TheCosmicNebula/ClioIVDigitalDash/4 - Software/3 - RealDash UI/images/car.jpg

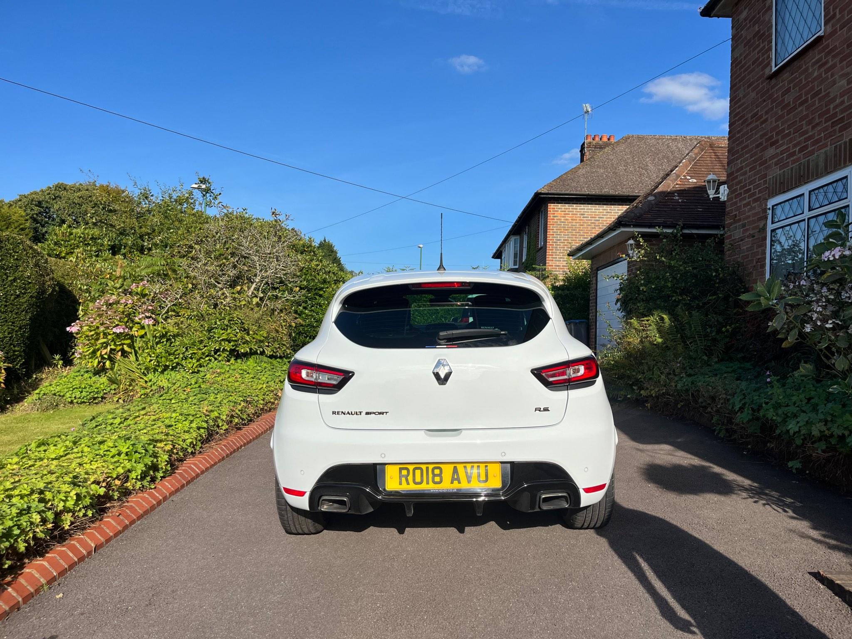
4 - Software/3 - RealDash UI/images/car.jpg
