TheCosmicNebula/ClioIVDigitalDash/1 - Physical Unit/1 - Pi/Raspberry-Pi-5-Technical-Drawing.jpg

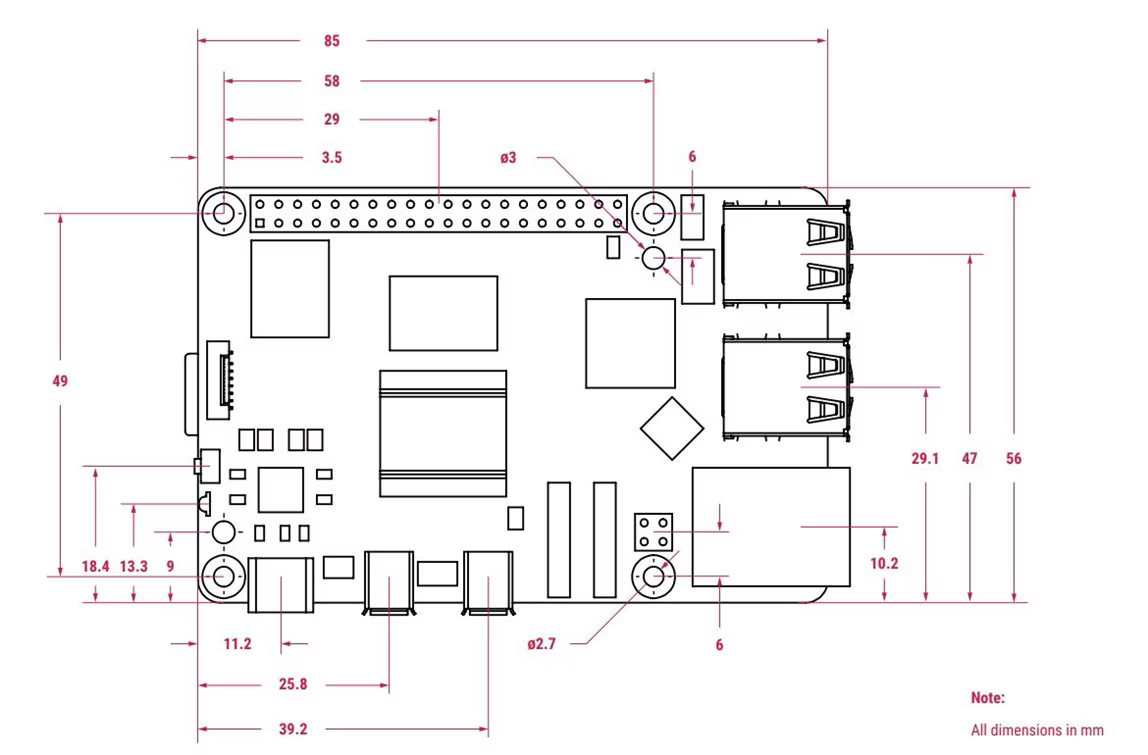
1 - Physical Unit/1 - Pi/Raspberry-Pi-5-Technical-Drawing.jpg
