TheCosmicNebula/ClioIVDigitalDash/1 - Physical Unit/3 - Label/561815/label.png

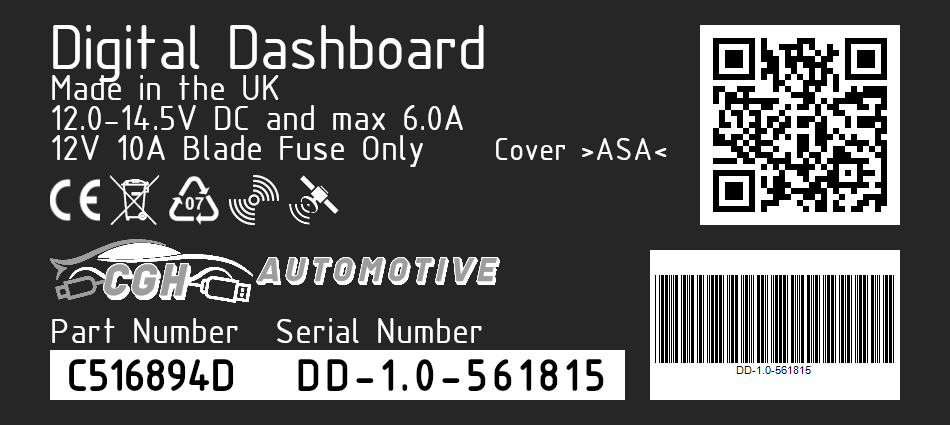
1 - Physical Unit/3 - Label/561815/label.png
