TheCosmicNebula/ClioIVDigitalDash/1 - Physical Unit/4 - Reference/rear.jpg

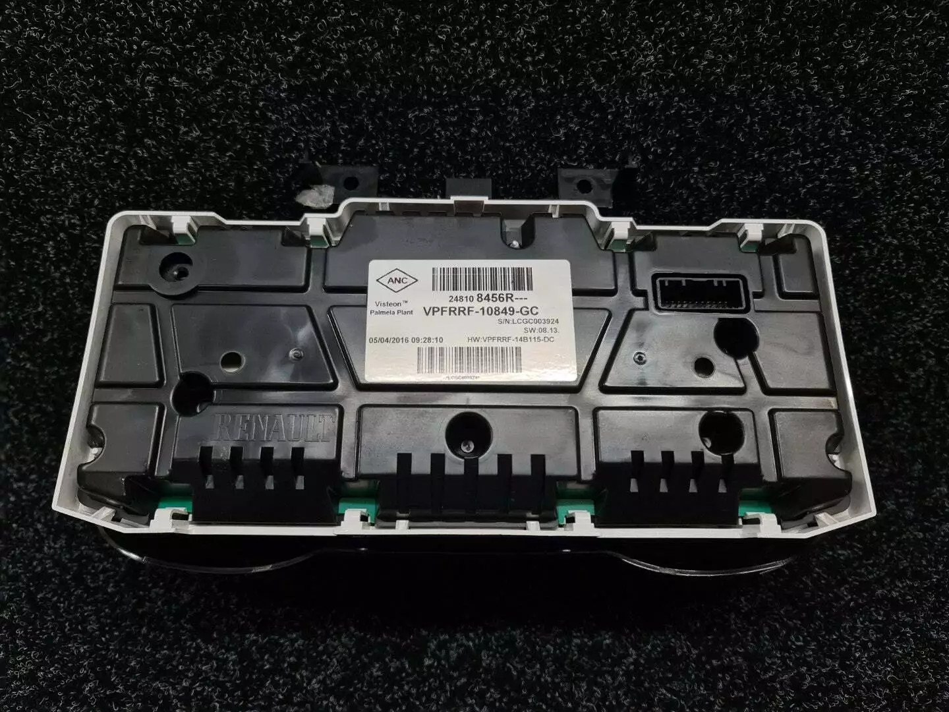
1 - Physical Unit/4 - Reference/rear.jpg
