TheCosmicNebula/ClioIVDigitalDash/2 - Custom UI/20240502_194230.jpg

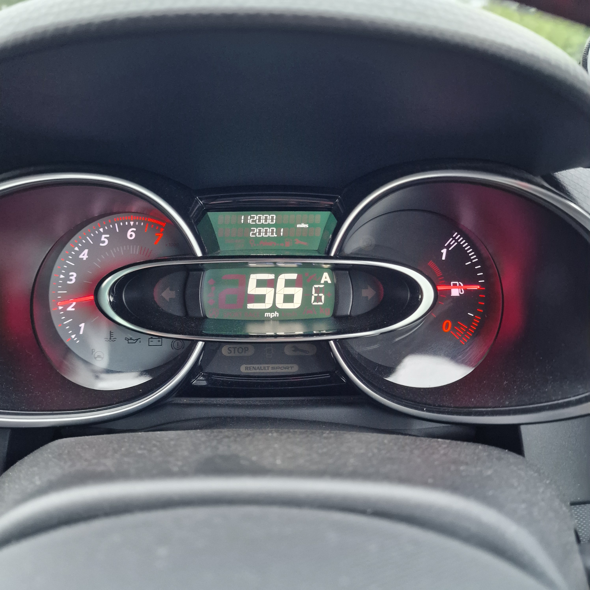
2 - Custom UI/20240502_194230.jpg
