TheCosmicNebula/ClioIVDigitalDash/2 - Custom UI/example_ui.jpg

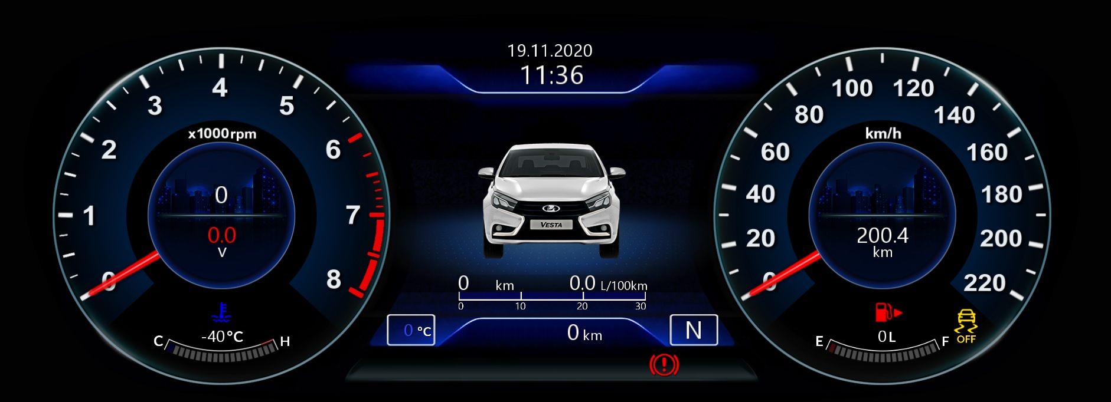
2 - Custom UI/example_ui.jpg
