TheCosmicNebula/ClioIVDigitalDash/2 - Custom UI/pixelcut-export.jpeg

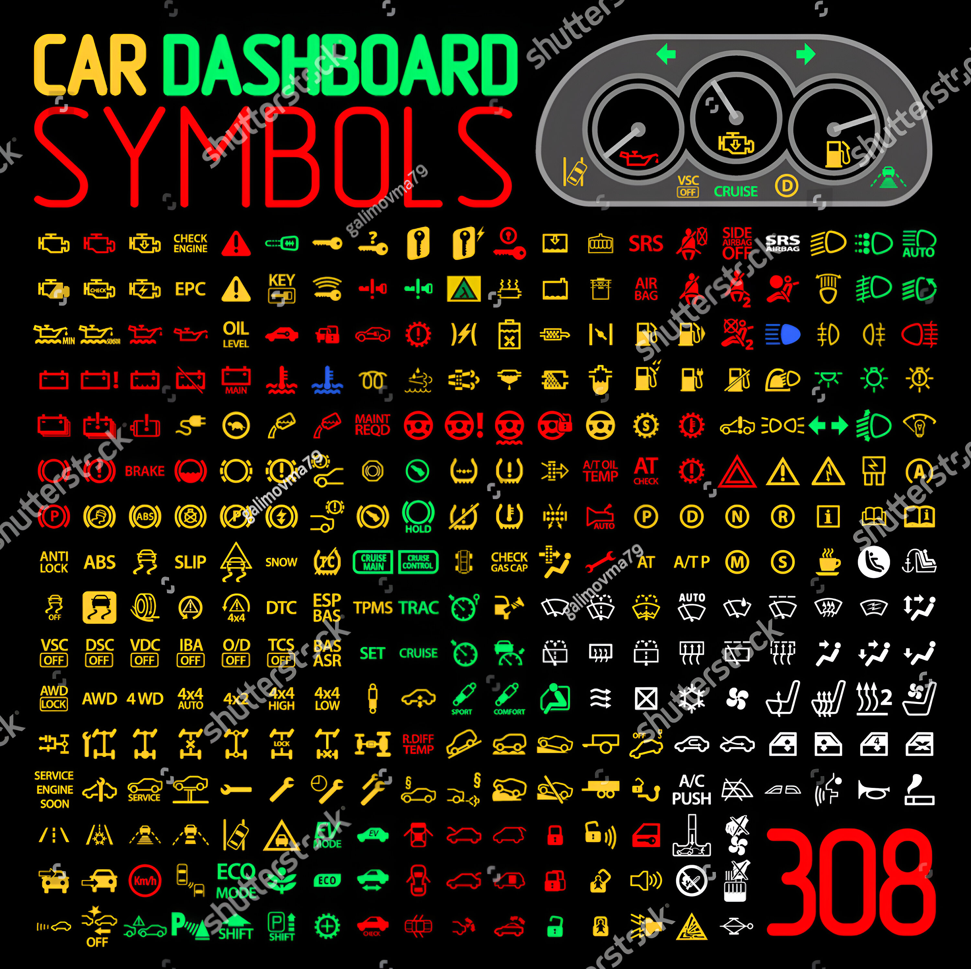
2 - Custom UI/pixelcut-export.jpeg
