TheCosmicNebula/ClioIVDigitalDash/2 - Custom UI/pixelcut-export.png

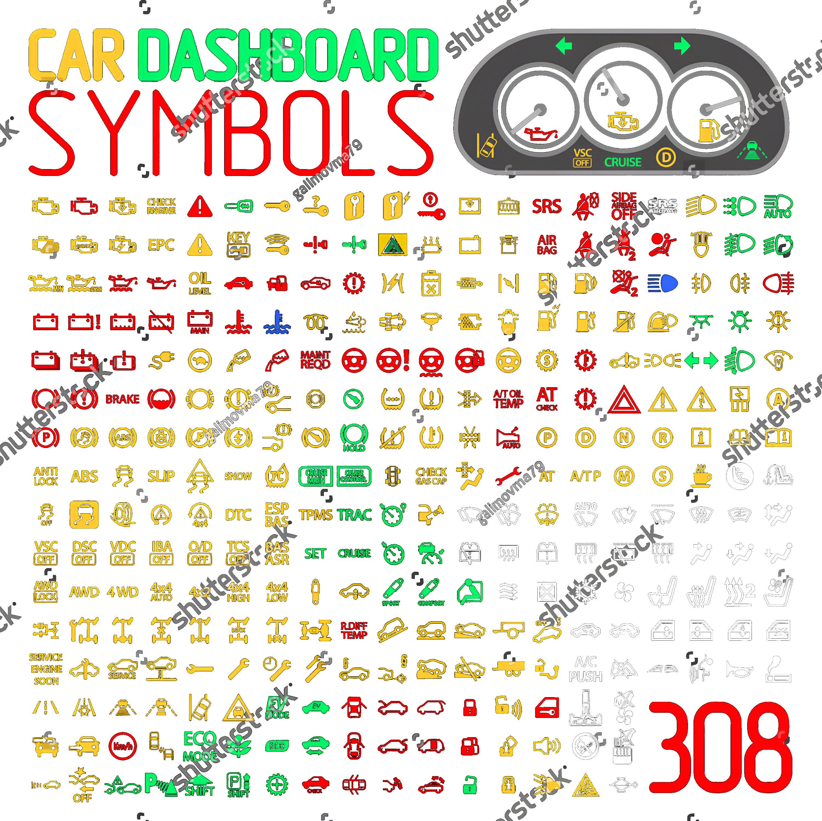
2 - Custom UI/pixelcut-export.png
