TheCosmicNebula/ClioIVDigitalDash/2 - Custom UI/vector-collection-car-dashboard-panel-600w-329151206.webp

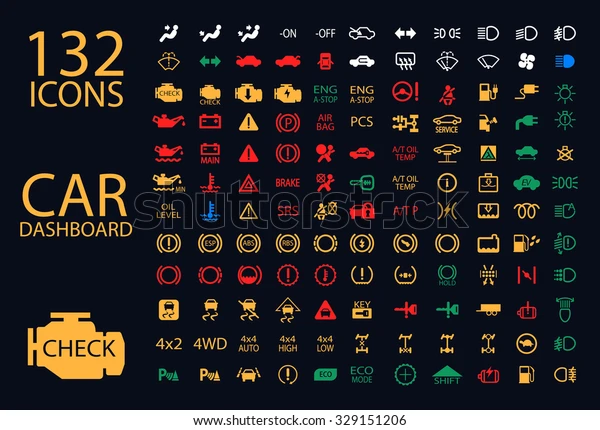
2 - Custom UI/vector-collection-car-dashboard-panel-600w-329151206.webp
