TheCosmicNebula/ClioIVDigitalDash/3 - Startup Animation/boot_darkmode_v2.gif

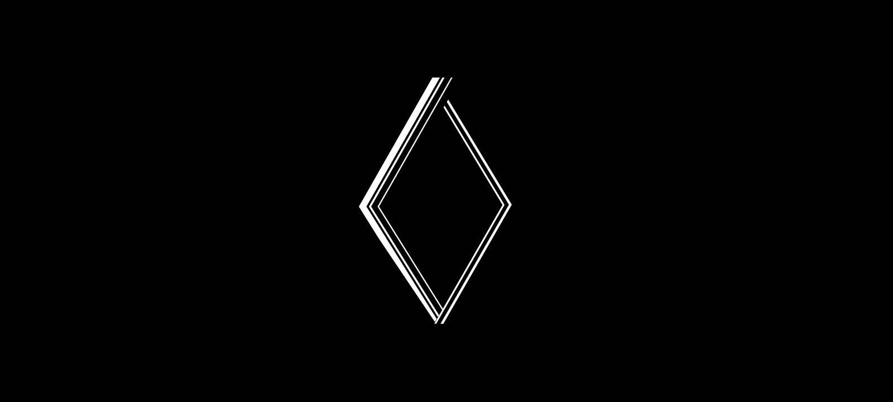
3 - Startup Animation/boot_darkmode_v2.gif
