TheCosmicNebula/ClioIVDigitalDash/3 - Startup Animation/cgh_automotive.png

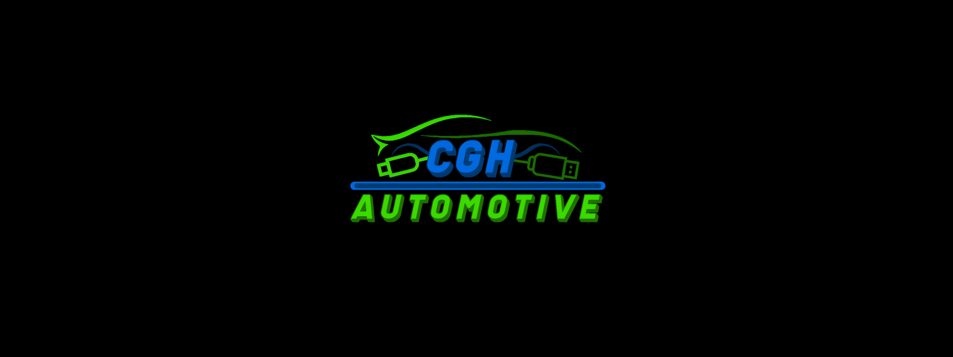
3 - Startup Animation/cgh_automotive.png
