TheCosmicNebula/ClioIVDigitalDash/3 - Startup Animation/reference/original_animation.gif

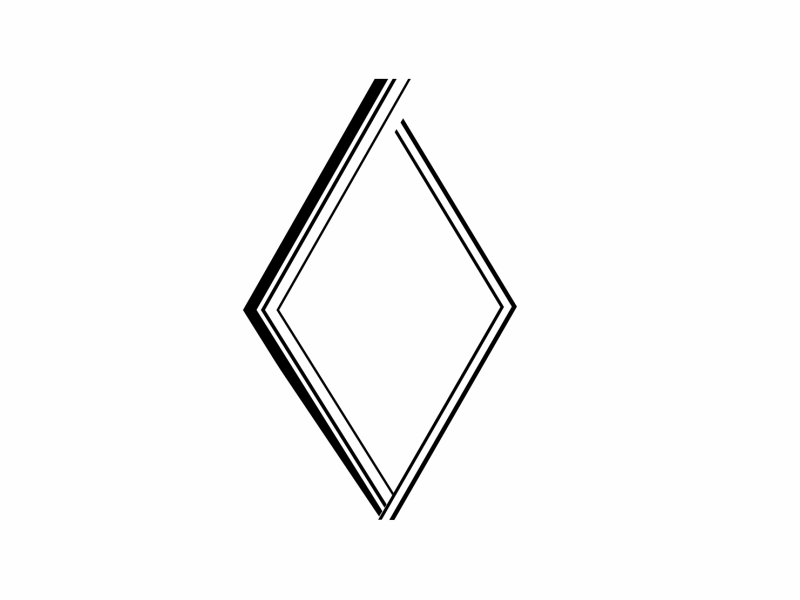
3 - Startup Animation/reference/original_animation.gif
