TheCosmicNebula/ClioIVDigitalDash/3 - Startup Animation/ss/boot_v1.gif

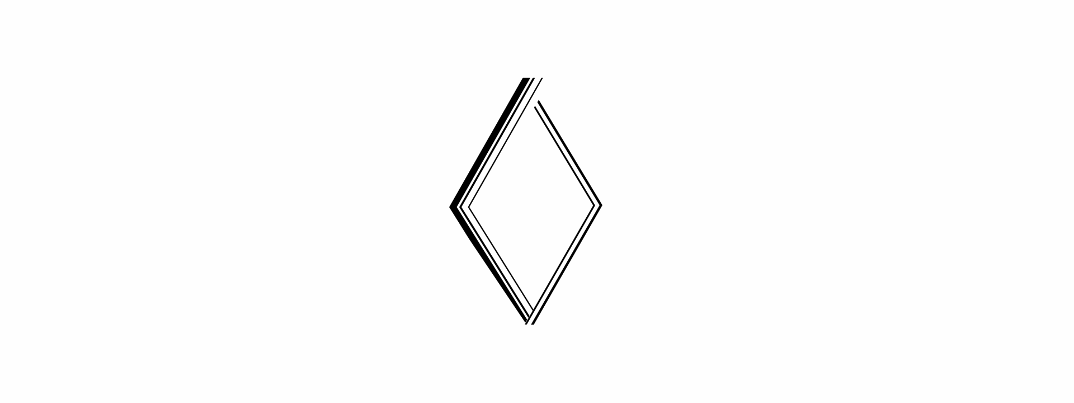
3 - Startup Animation/ss/boot_v1.gif
