TheCosmicNebula/ClioIVDigitalDash/3 - Startup Animation/TheCN.png

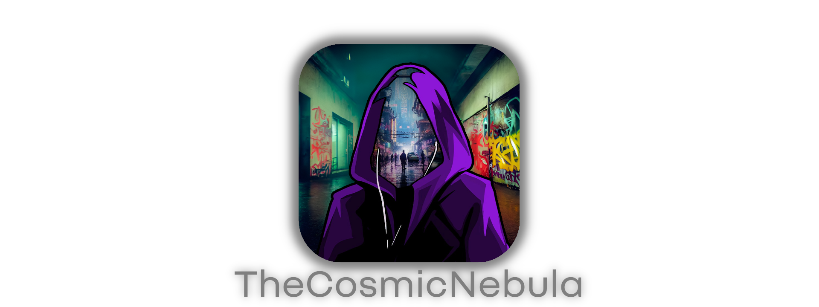
3 - Startup Animation/TheCN.png
