TheCosmicNebula/ClioIVDigitalDash/4 - Software/3 - RealDash UI/images/cruise_control.png

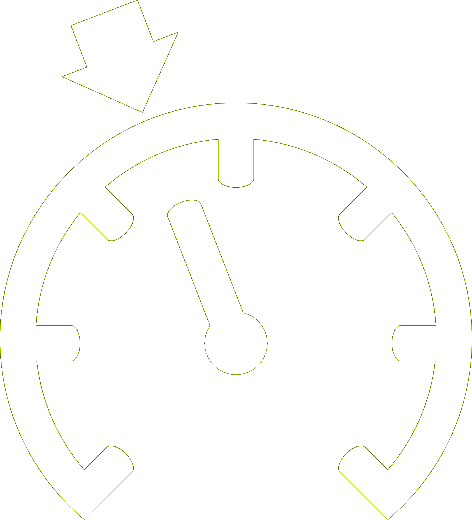
4 - Software/3 - RealDash UI/images/cruise_control.png
