TheCosmicNebula/ClioIVDigitalDash/4 - Software/3 - RealDash UI/images/Cruise_Control.svg.png

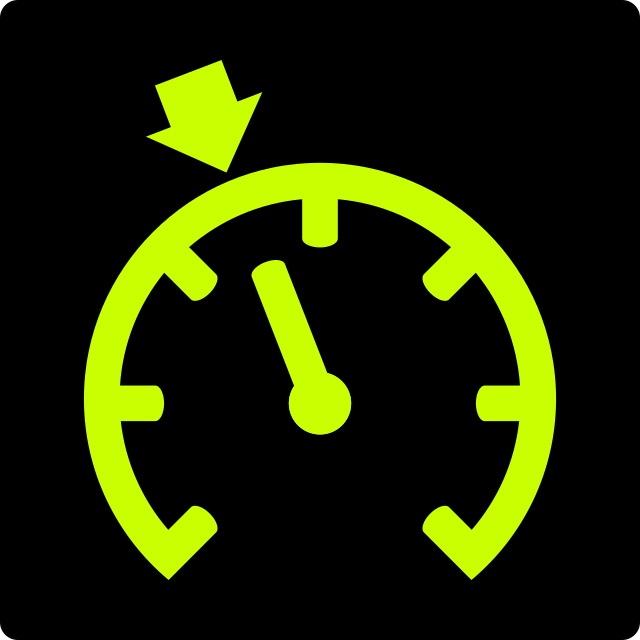
4 - Software/3 - RealDash UI/images/Cruise_Control.svg.png
