TheCosmicNebula/ClioIVDigitalDash/4 - Software/3 - RealDash UI/images/final/abs.png

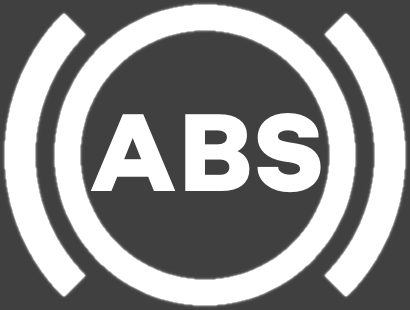
4 - Software/3 - RealDash UI/images/final/abs.png
