TheCosmicNebula/ClioIVDigitalDash/4 - Software/3 - RealDash UI/images/final/airbag.png

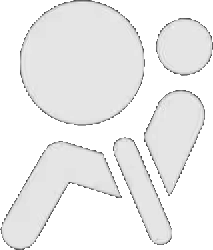
4 - Software/3 - RealDash UI/images/final/airbag.png
