TheCosmicNebula/ClioIVDigitalDash/4 - Software/3 - RealDash UI/images/final/auto_lights.png

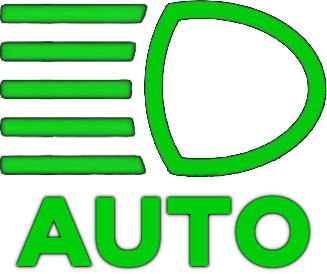
4 - Software/3 - RealDash UI/images/final/auto_lights.png
