TheCosmicNebula/ClioIVDigitalDash/4 - Software/3 - RealDash UI/images/final/auto_wipers.png

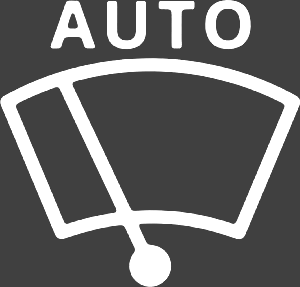
4 - Software/3 - RealDash UI/images/final/auto_wipers.png
