TheCosmicNebula/ClioIVDigitalDash/4 - Software/3 - RealDash UI/images/final/battery.png

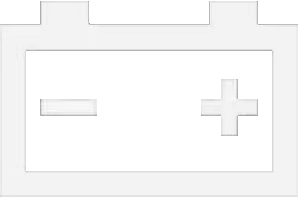
4 - Software/3 - RealDash UI/images/final/battery.png
