TheCosmicNebula/ClioIVDigitalDash/4 - Software/3 - RealDash UI/images/final/car_body.png

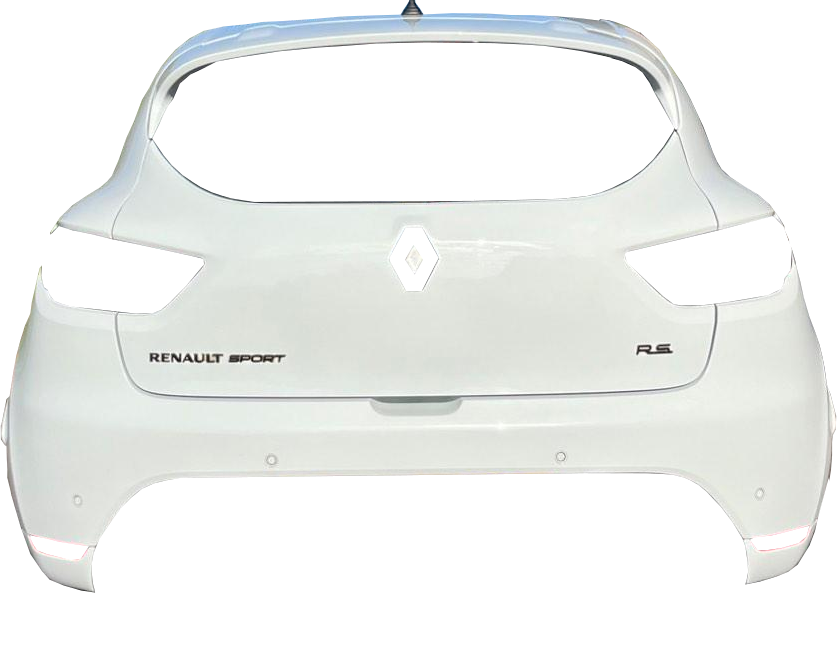
4 - Software/3 - RealDash UI/images/final/car_body.png
