TheCosmicNebula/ClioIVDigitalDash/4 - Software/3 - RealDash UI/images/final/check_engine.png

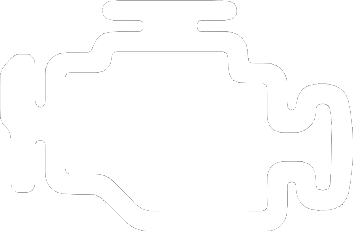
4 - Software/3 - RealDash UI/images/final/check_engine.png
