TheCosmicNebula/ClioIVDigitalDash/4 - Software/3 - RealDash UI/images/final/coolant_temp.png

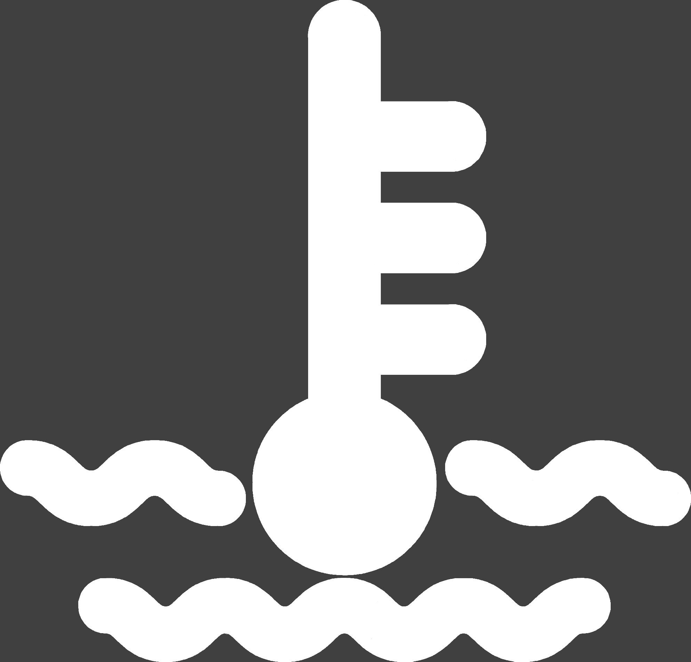
4 - Software/3 - RealDash UI/images/final/coolant_temp.png
