TheCosmicNebula/ClioIVDigitalDash/4 - Software/3 - RealDash UI/images/final/door_ajar.png

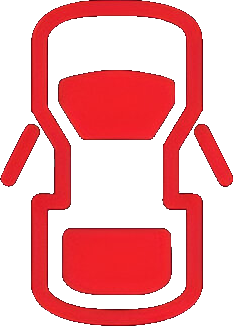
4 - Software/3 - RealDash UI/images/final/door_ajar.png
