TheCosmicNebula/ClioIVDigitalDash/4 - Software/3 - RealDash UI/images/final/door_ajar_4.png

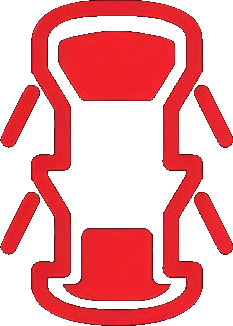
4 - Software/3 - RealDash UI/images/final/door_ajar_4.png
