TheCosmicNebula/ClioIVDigitalDash/4 - Software/3 - RealDash UI/images/final/door_ajar_boot_open.png

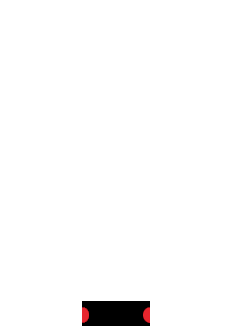
4 - Software/3 - RealDash UI/images/final/door_ajar_boot_open.png
