TheCosmicNebula/ClioIVDigitalDash/4 - Software/3 - RealDash UI/images/final/door_ajar_nsf_open.png

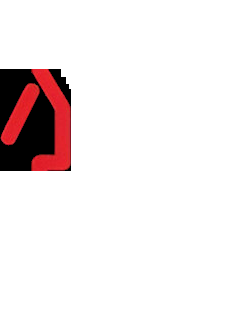
4 - Software/3 - RealDash UI/images/final/door_ajar_nsf_open.png
