TheCosmicNebula/ClioIVDigitalDash/4 - Software/3 - RealDash UI/images/final/esc_off.png

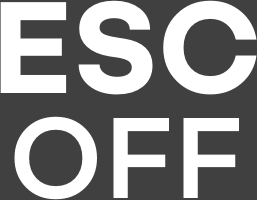
4 - Software/3 - RealDash UI/images/final/esc_off.png
