TheCosmicNebula/ClioIVDigitalDash/4 - Software/3 - RealDash UI/images/final/front_defrost.png

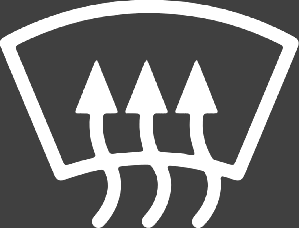
4 - Software/3 - RealDash UI/images/final/front_defrost.png
