TheCosmicNebula/ClioIVDigitalDash/4 - Software/3 - RealDash UI/images/final/front_fog.png

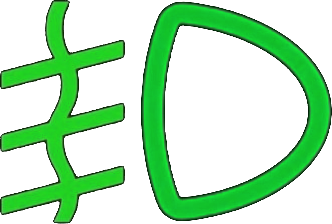
4 - Software/3 - RealDash UI/images/final/front_fog.png
