TheCosmicNebula/ClioIVDigitalDash/4 - Software/3 - RealDash UI/images/final/fuel.png

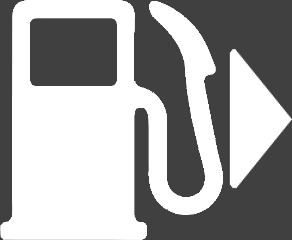
4 - Software/3 - RealDash UI/images/final/fuel.png
