TheCosmicNebula/ClioIVDigitalDash/4 - Software/3 - RealDash UI/images/final/fuel_low.png

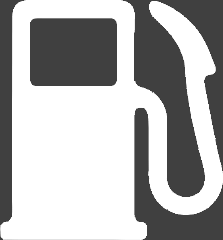
4 - Software/3 - RealDash UI/images/final/fuel_low.png
