TheCosmicNebula/ClioIVDigitalDash/4 - Software/3 - RealDash UI/images/final/handbrake.png

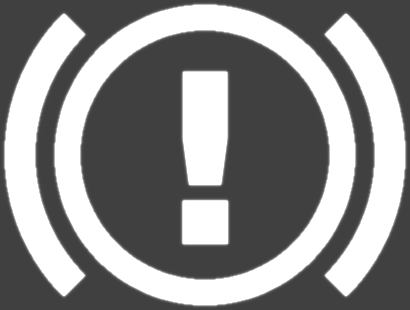
4 - Software/3 - RealDash UI/images/final/handbrake.png
