TheCosmicNebula/ClioIVDigitalDash/4 - Software/3 - RealDash UI/images/final/ice_warning.png

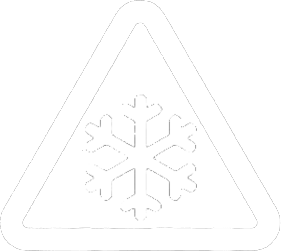
4 - Software/3 - RealDash UI/images/final/ice_warning.png
