TheCosmicNebula/ClioIVDigitalDash/4 - Software/3 - RealDash UI/images/final/lock.png

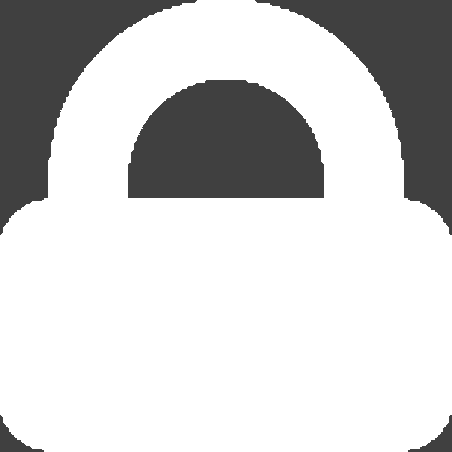
4 - Software/3 - RealDash UI/images/final/lock.png
