TheCosmicNebula/ClioIVDigitalDash/4 - Software/3 - RealDash UI/images/final/low_beam.png

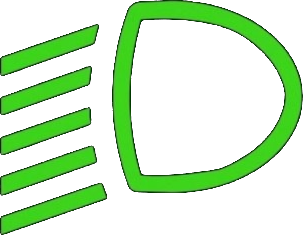
4 - Software/3 - RealDash UI/images/final/low_beam.png
