TheCosmicNebula/ClioIVDigitalDash/4 - Software/3 - RealDash UI/images/final/oil_pressure_w.png

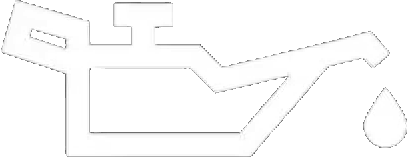
4 - Software/3 - RealDash UI/images/final/oil_pressure_w.png
