TheCosmicNebula/ClioIVDigitalDash/4 - Software/3 - RealDash UI/images/final/press_brake.png

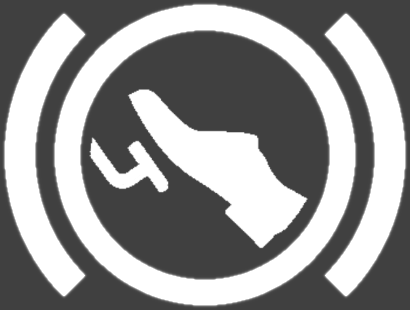
4 - Software/3 - RealDash UI/images/final/press_brake.png
