TheCosmicNebula/ClioIVDigitalDash/4 - Software/3 - RealDash UI/images/final/rear_defrost.png

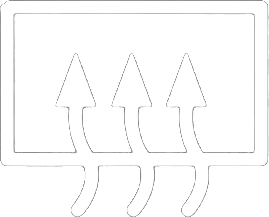
4 - Software/3 - RealDash UI/images/final/rear_defrost.png
