TheCosmicNebula/ClioIVDigitalDash/4 - Software/3 - RealDash UI/images/final/rear_fog.png

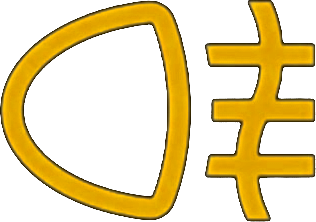
4 - Software/3 - RealDash UI/images/final/rear_fog.png
