TheCosmicNebula/ClioIVDigitalDash/4 - Software/3 - RealDash UI/images/final/rear_window_lock.png

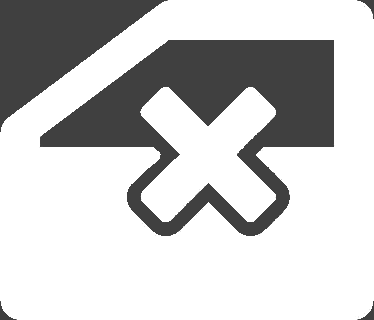
4 - Software/3 - RealDash UI/images/final/rear_window_lock.png
