TheCosmicNebula/ClioIVDigitalDash/4 - Software/3 - RealDash UI/images/final/renault_sport.png

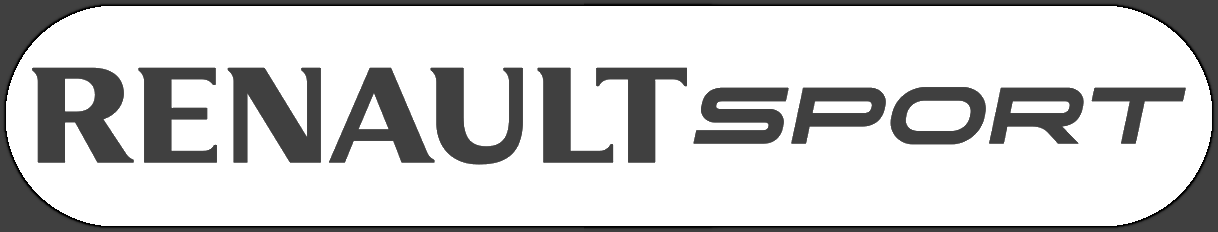
4 - Software/3 - RealDash UI/images/final/renault_sport.png
