TheCosmicNebula/ClioIVDigitalDash/4 - Software/3 - RealDash UI/images/final/seatbelt.png

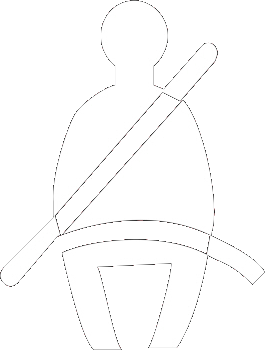
4 - Software/3 - RealDash UI/images/final/seatbelt.png
