TheCosmicNebula/ClioIVDigitalDash/4 - Software/3 - RealDash UI/images/final/side_lights.png

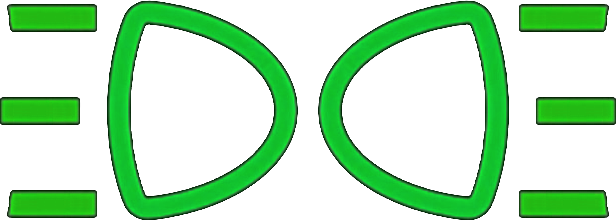
4 - Software/3 - RealDash UI/images/final/side_lights.png
