TheCosmicNebula/ClioIVDigitalDash/4 - Software/3 - RealDash UI/images/final/spanner.png

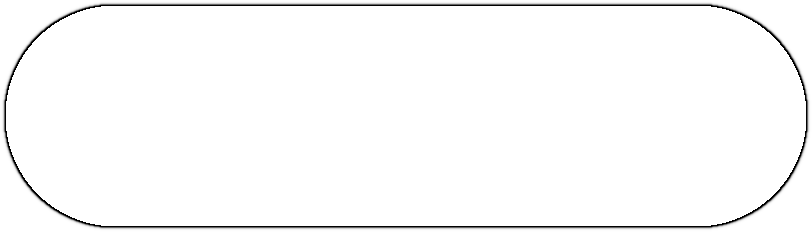
4 - Software/3 - RealDash UI/images/final/spanner.png
