TheCosmicNebula/ClioIVDigitalDash/4 - Software/3 - RealDash UI/images/final/steering.png

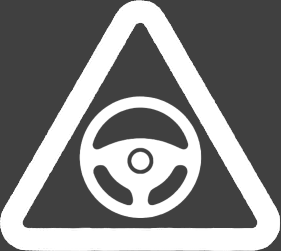
4 - Software/3 - RealDash UI/images/final/steering.png
