TheCosmicNebula/ClioIVDigitalDash/4 - Software/3 - RealDash UI/images/final/traction.png

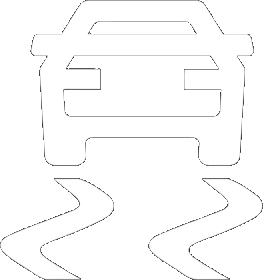
4 - Software/3 - RealDash UI/images/final/traction.png
