TheCosmicNebula/ClioIVDigitalDash/4 - Software/3 - RealDash UI/images/final/tyre_pressure.png

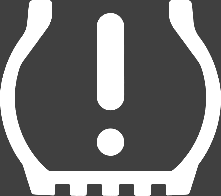
4 - Software/3 - RealDash UI/images/final/tyre_pressure.png
