TheCosmicNebula/ClioIVDigitalDash/4 - Software/3 - RealDash UI/images/source/arrows.webp

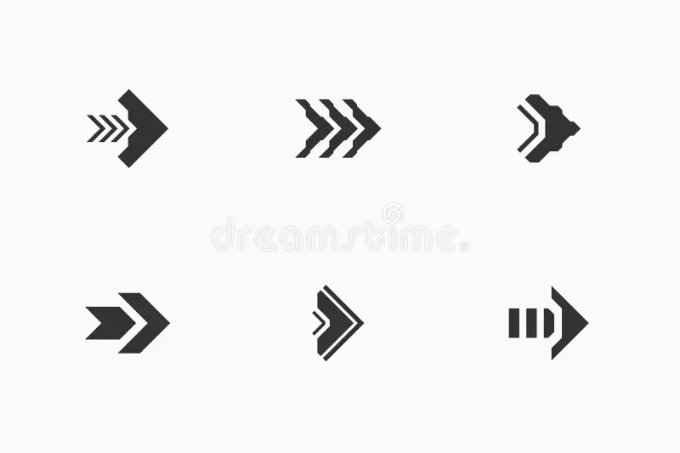
4 - Software/3 - RealDash UI/images/source/arrows.webp
