TheCosmicNebula/ClioIVDigitalDash/4 - Software/3 - RealDash UI/images/source/coolant_temperature.jpg

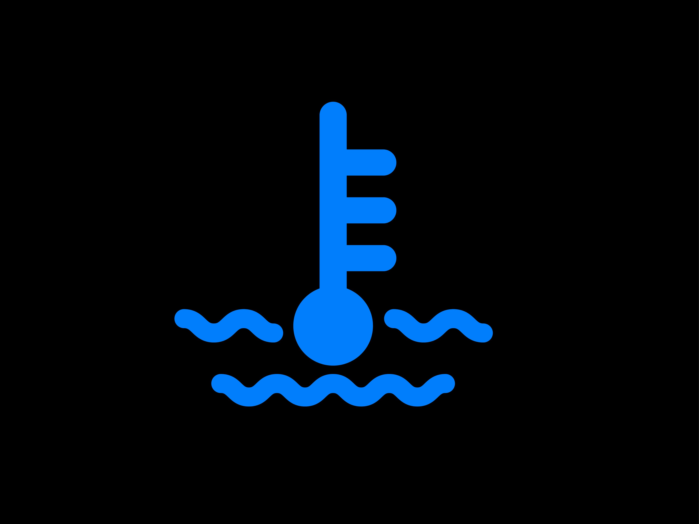
4 - Software/3 - RealDash UI/images/source/coolant_temperature.jpg
