TheCosmicNebula/ClioIVDigitalDash/4 - Software/3 - RealDash UI/images/source/door_adjar_a.jpeg

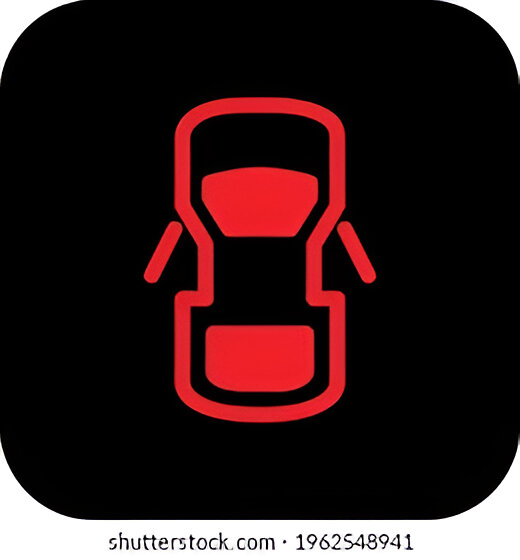
4 - Software/3 - RealDash UI/images/source/door_adjar_a.jpeg
