TheCosmicNebula/ClioIVDigitalDash/4 - Software/3 - RealDash UI/images/source/lock.png

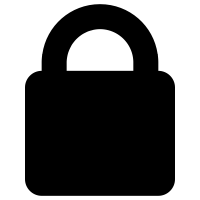
4 - Software/3 - RealDash UI/images/source/lock.png
