TheCosmicNebula/ClioIVDigitalDash/4 - Software/3 - RealDash UI/images/source/press_brake.webp

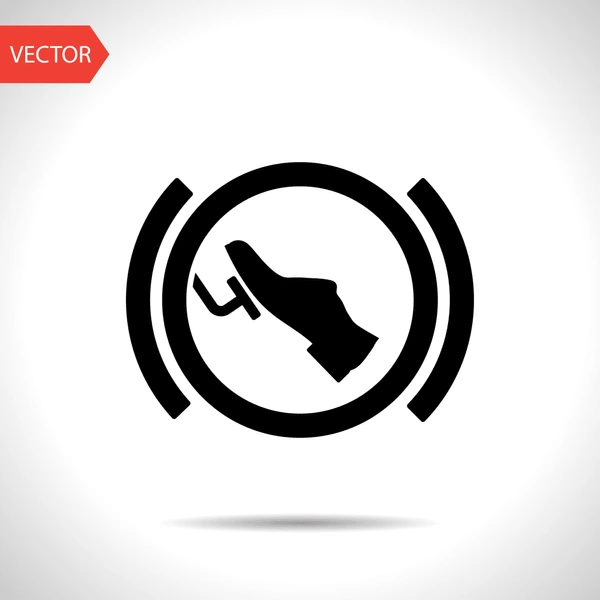
4 - Software/3 - RealDash UI/images/source/press_brake.webp
