TheCosmicNebula/ClioIVDigitalDash/4 - Software/3 - RealDash UI/images/source/renault-sport-sticker.png

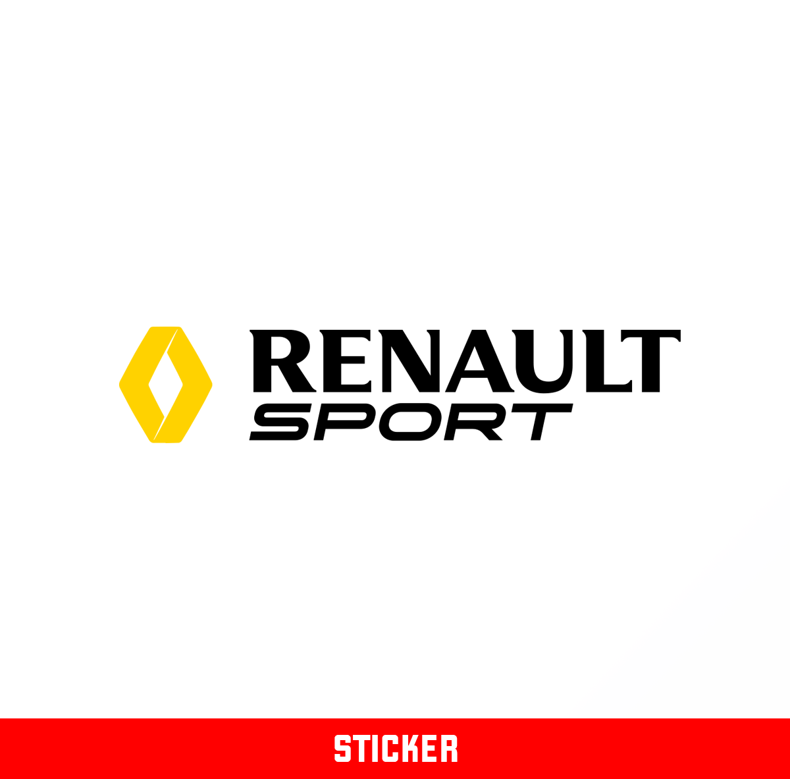
4 - Software/3 - RealDash UI/images/source/renault-sport-sticker.png
