TheCosmicNebula/ClioIVDigitalDash/4 - Software/3 - RealDash UI/images/source/window_lock.webp

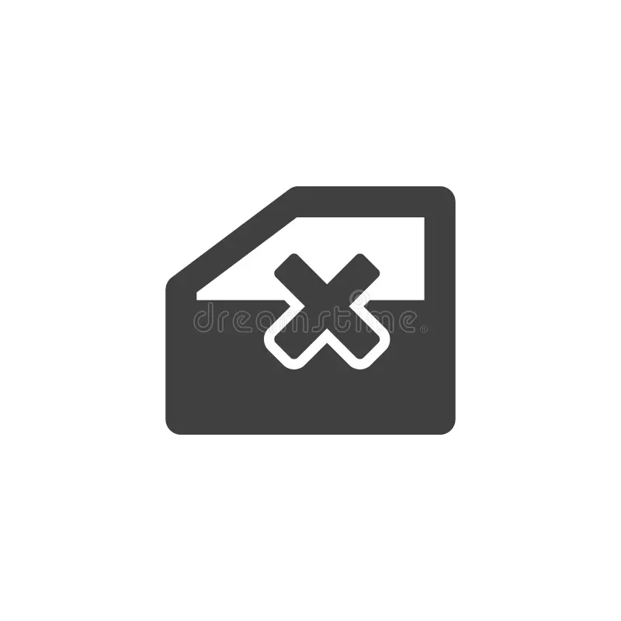
4 - Software/3 - RealDash UI/images/source/window_lock.webp
