TheCosmicNebula/ClioIVDigitalDash/4 - Software/3 - RealDash UI/images/source/wrench.jpg

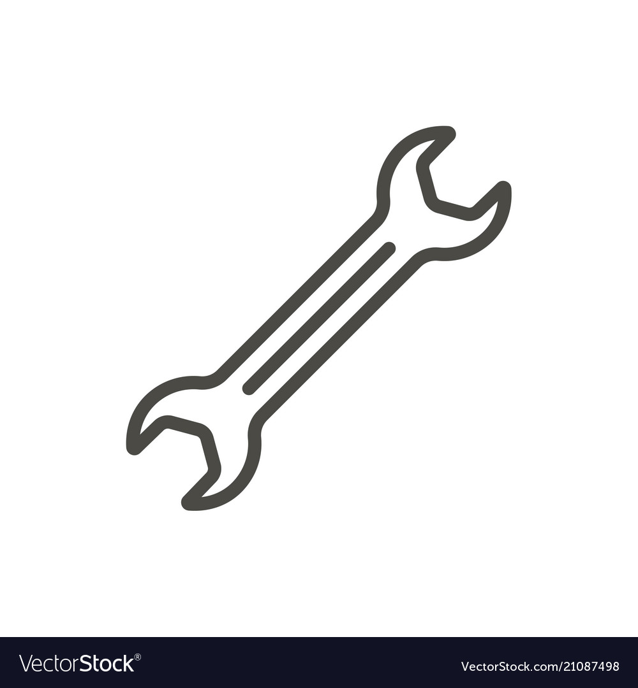
4 - Software/3 - RealDash UI/images/source/wrench.jpg
