TheCosmicNebula/ClioIVDigitalDash/4 - Software/3 - RealDash UI/images/source/zref_1.jpg

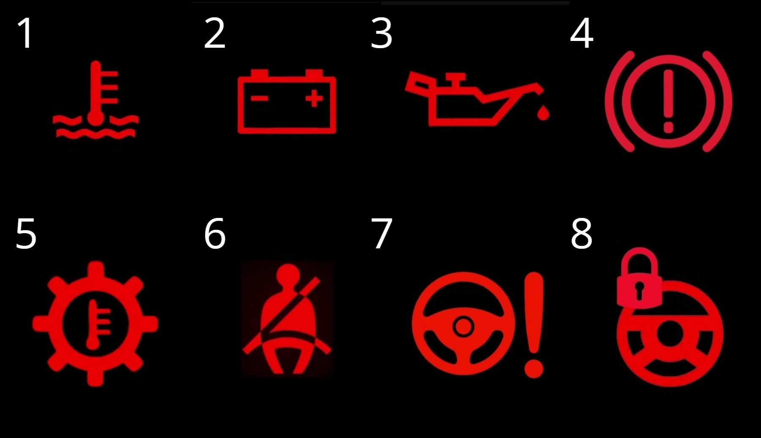
4 - Software/3 - RealDash UI/images/source/zref_1.jpg
