TheCosmicNebula/ClioIVDigitalDash/4 - Software/3 - RealDash UI/images/source/zref_9.jpg

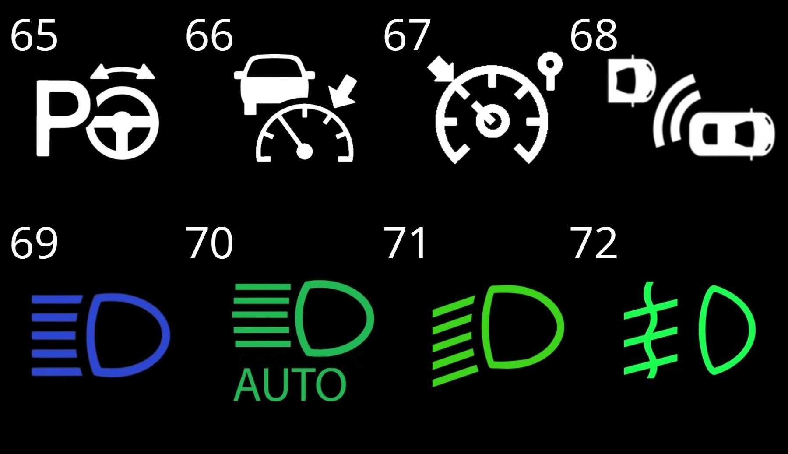
4 - Software/3 - RealDash UI/images/source/zref_9.jpg
