TheCosmicNebula/ClioIVDigitalDash/4 - Software/3 - RealDash UI/images/source/zref_11a.jpeg

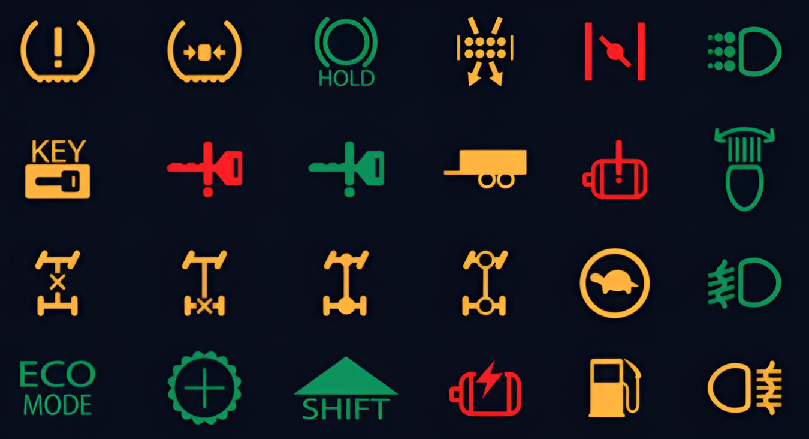
4 - Software/3 - RealDash UI/images/source/zref_11a.jpeg
