TheCosmicNebula/ClioIVDigitalDash/4 - Software/3 - RealDash UI/images/ss/abs.png

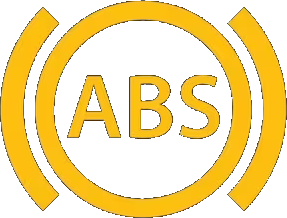
4 - Software/3 - RealDash UI/images/ss/abs.png
