TheCosmicNebula/ClioIVDigitalDash/4 - Software/3 - RealDash UI/images/ss/coolant_temp_cold.png

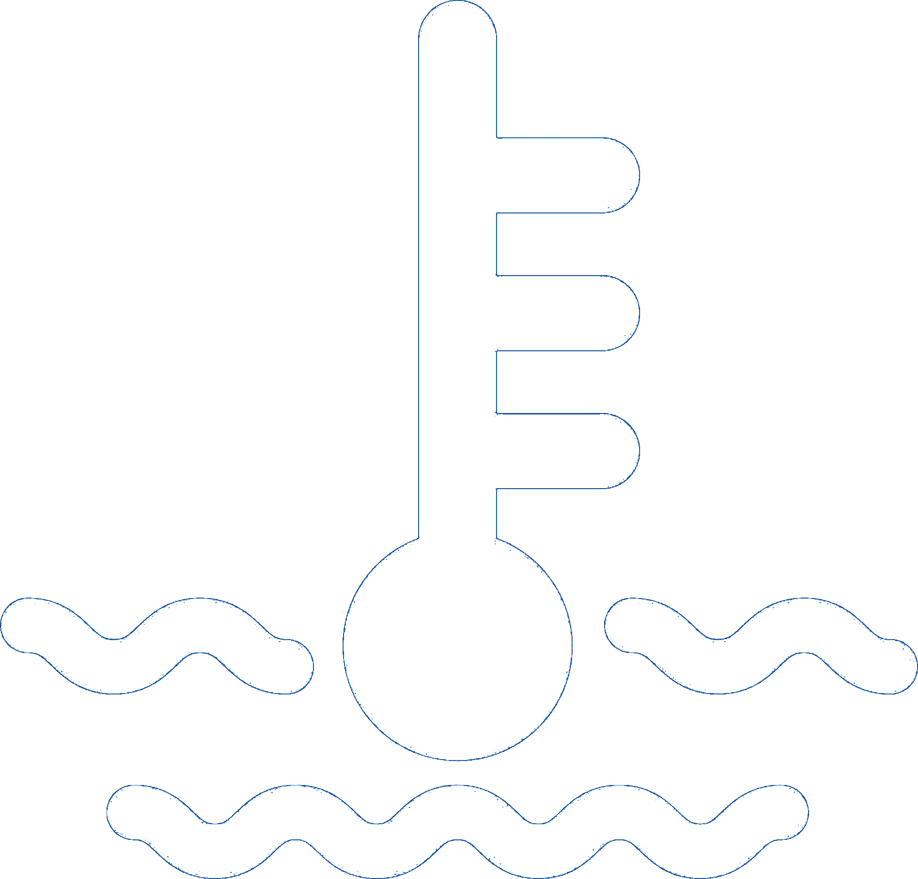
4 - Software/3 - RealDash UI/images/ss/coolant_temp_cold.png
