TheCosmicNebula/ClioIVDigitalDash/4 - Software/3 - RealDash UI/images/ss/esp_off.png

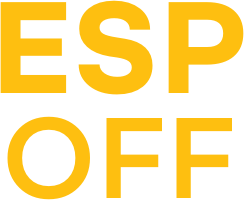
4 - Software/3 - RealDash UI/images/ss/esp_off.png
