TheCosmicNebula/ClioIVDigitalDash/4 - Software/3 - RealDash UI/images/ss/press_brake_pedal.png

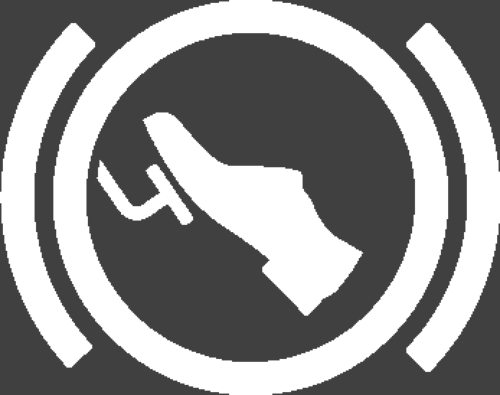
4 - Software/3 - RealDash UI/images/ss/press_brake_pedal.png
