TheCosmicNebula/ClioIVDigitalDash/1 - Physical Unit/3 - Label/components/EU-waste.webp

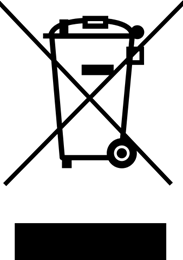
1 - Physical Unit/3 - Label/components/EU-waste.webp
