TheCosmicNebula/ClioIVDigitalDash/1 - Physical Unit/3 - Label/components/pngtree-signals-business-radio-system-vector-png-image_40955204.jpg

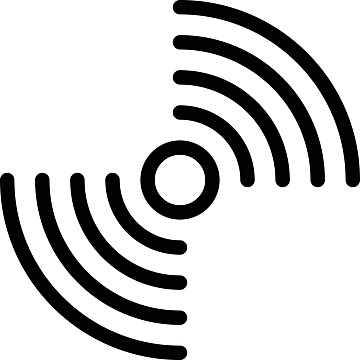
1 - Physical Unit/3 - Label/components/pngtree-signals-business-radio-system-vector-png-image_40955204.jpg
