TheCosmicNebula/ClioIVDigitalDash/1 - Physical Unit/9 - Prototype/connector_clamp.stl

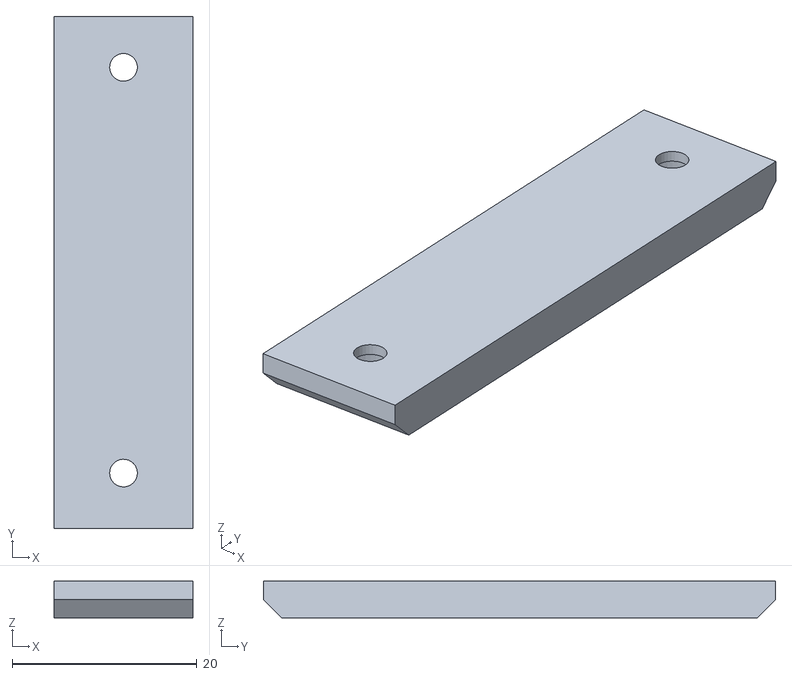
[picture p105: CAD file, 2024-09-08]
1 - Physical Unit/9 - Prototype/connector_clamp.stl
15.0 x 55.4 x 4.00
