TheCosmicNebula/ClioIVDigitalDash/1 - Physical Unit/9 - Prototype/ss/rear_plate_v1.stl

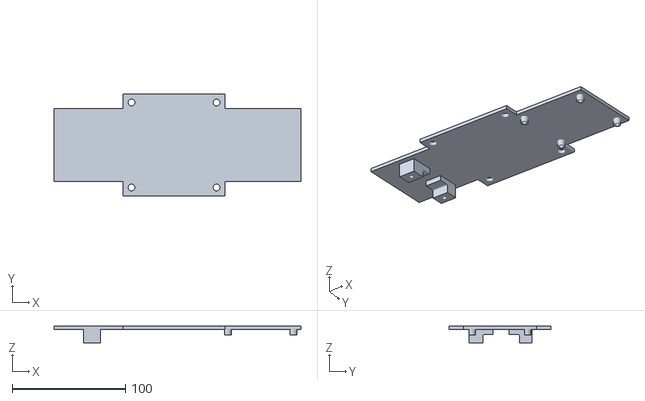
[picture p106: CAD file, 2024-09-08]
1 - Physical Unit/9 - Prototype/ss/rear_plate_v1.stl
218.0 x 90.0 x 14.9
