TheCosmicNebula/ClioIVDigitalDash/1 - Physical Unit/0 - Casing/plate_left_v14.stl

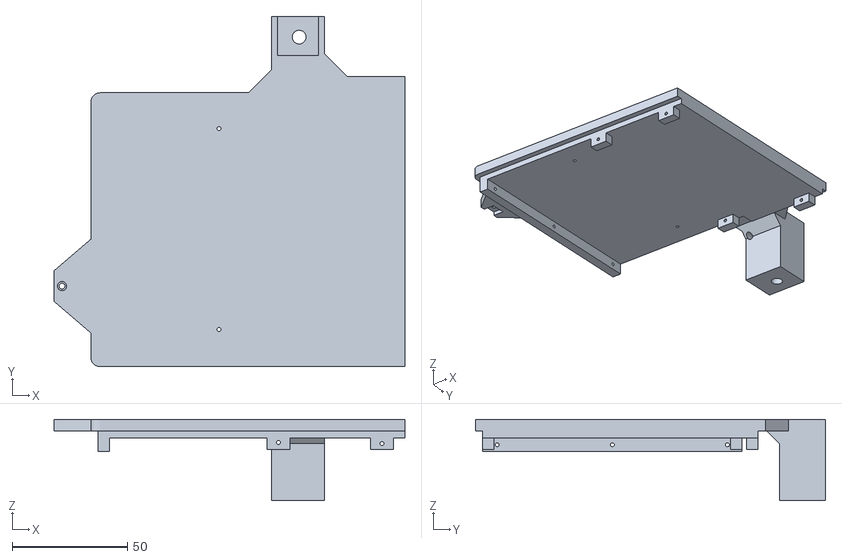
[picture p107: CAD file, 2024-10-02]
1 - Physical Unit/0 - Casing/plate_left_v14.stl
152.5 x 152.2 x 35.2
