TheCosmicNebula/ClioIVDigitalDash/1 - Physical Unit/0 - Casing/frame_right_bottom_v1.stl

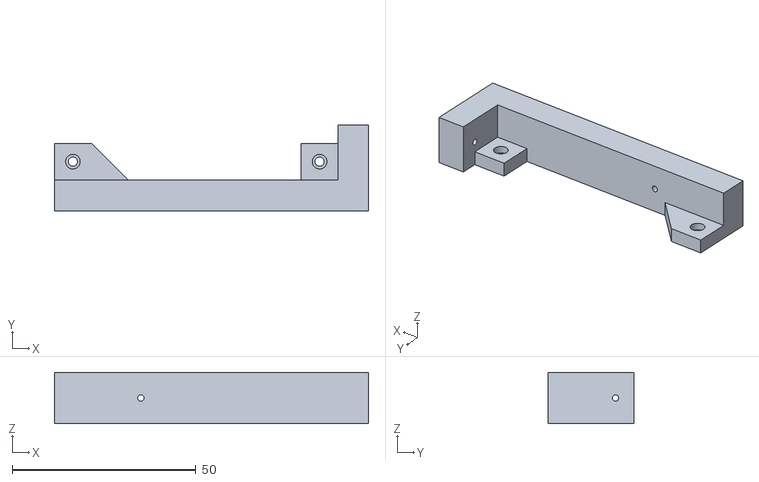
[picture p108: CAD file, 2024-09-28]
1 - Physical Unit/0 - Casing/frame_right_bottom_v1.stl
85.4 x 23.4 x 14.0
