TheCosmicNebula/ClioIVDigitalDash/1 - Physical Unit/0 - Casing/frame_right_top_v1.stl

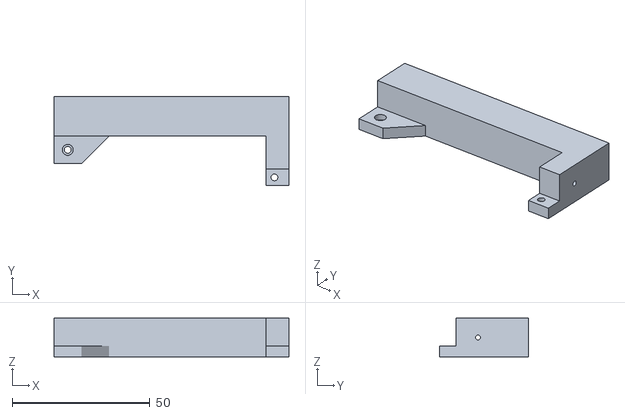
[picture p109: CAD file, 2024-09-28]
1 - Physical Unit/0 - Casing/frame_right_top_v1.stl
85.4 x 32.4 x 14.0
