TheCosmicNebula/ClioIVDigitalDash/1 - Physical Unit/0 - Casing/rear_shell_right_v9.stl

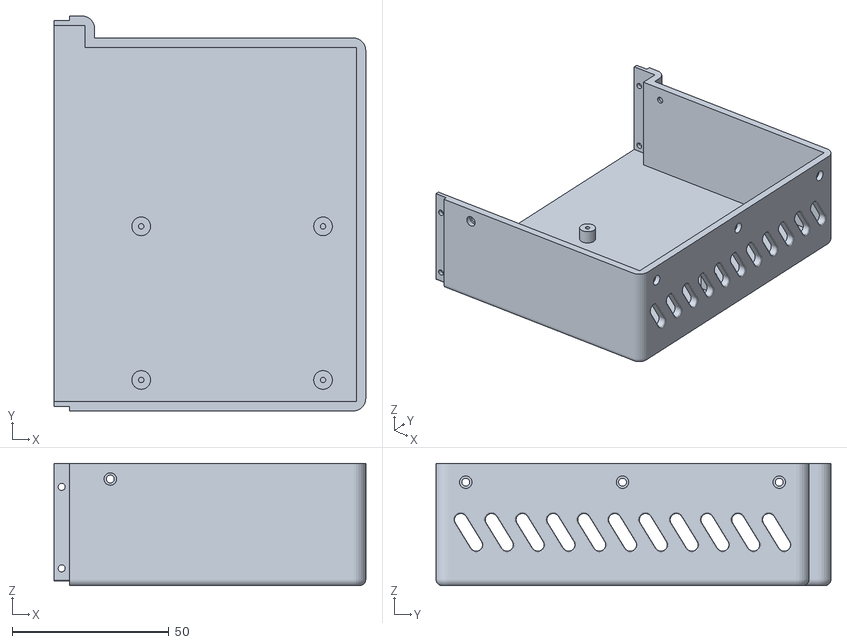
[picture p110: CAD file, 2024-09-28]
1 - Physical Unit/0 - Casing/rear_shell_right_v9.stl
99.4 x 126.0 x 39.0
