TheCosmicNebula/ClioIVDigitalDash/1 - Physical Unit/0 - Casing/frame_left_v1.stl

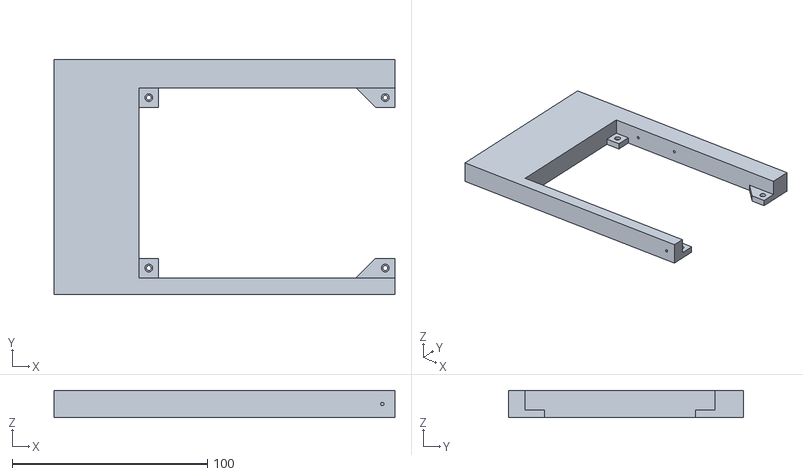
[picture p111: CAD file, 2024-09-28]
1 - Physical Unit/0 - Casing/frame_left_v1.stl
174.7 x 120.2 x 14.0
