TheCosmicNebula/ClioIVDigitalDash/1 - Physical Unit/0 - Casing/frame_clamp_v1.stl

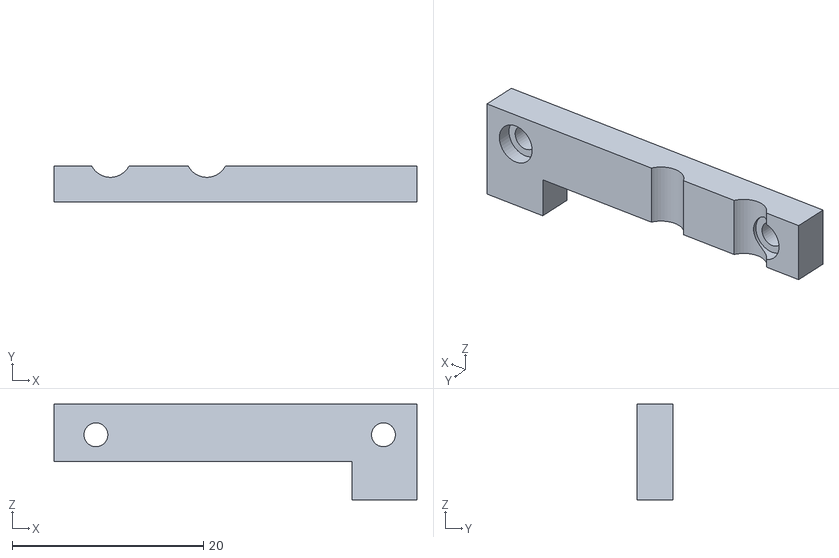
[picture p112: CAD file, 2024-09-28]
1 - Physical Unit/0 - Casing/frame_clamp_v1.stl
38.0 x 3.80 x 10.00
