TheCosmicNebula/ClioIVDigitalDash/1 - Physical Unit/0 - Casing/back_cover_left_v4.stl

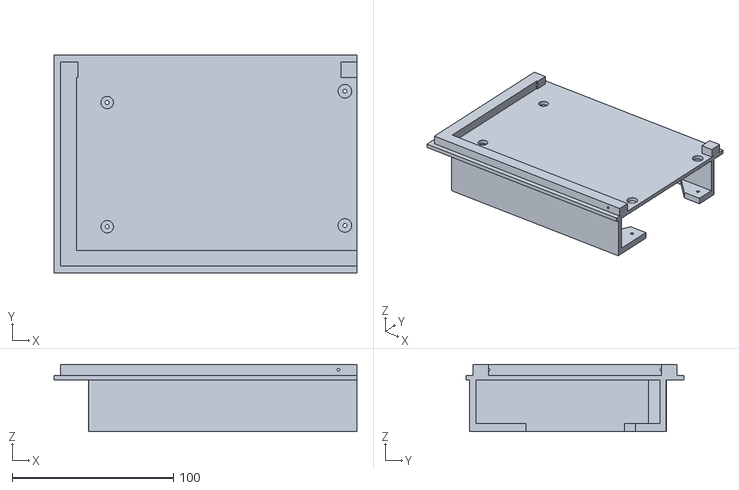
[picture p113: CAD file, 2024-09-20]
1 - Physical Unit/0 - Casing/back_cover_left_v4.stl
187.9 x 135.0 x 41.7
