TheCosmicNebula/ClioIVDigitalDash/1 - Physical Unit/0 - Casing/back_cover_right_v4.stl

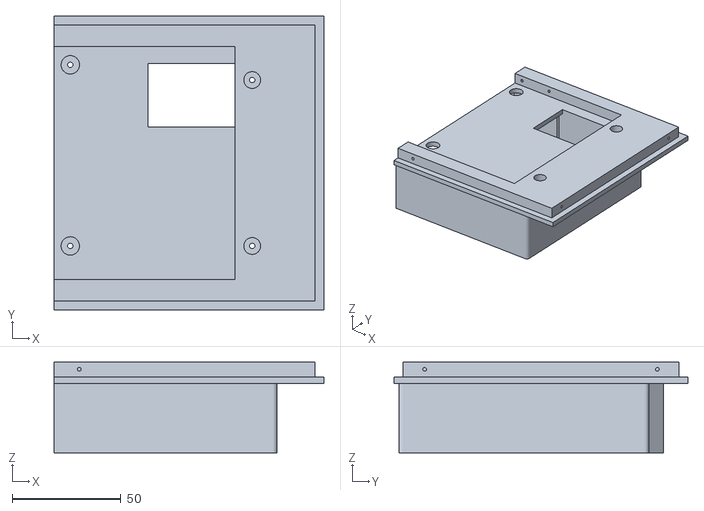
[picture p114: CAD file, 2024-09-20]
1 - Physical Unit/0 - Casing/back_cover_right_v4.stl
124.1 x 135.0 x 41.7
