TheCosmicNebula/ClioIVDigitalDash/1 - Physical Unit/0 - Casing/rear_shell_left_v9.stl

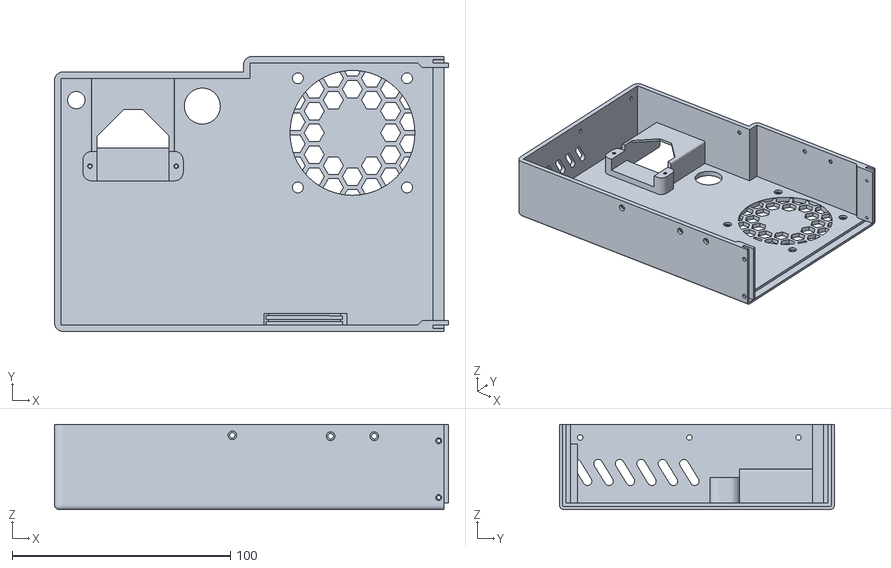
[picture p115: CAD file, 2024-09-20]
1 - Physical Unit/0 - Casing/rear_shell_left_v9.stl
180.5 x 126.0 x 39.0
