TheCosmicNebula/ClioIVDigitalDash/1 - Physical Unit/0 - Casing/connector_retention_v4.stl

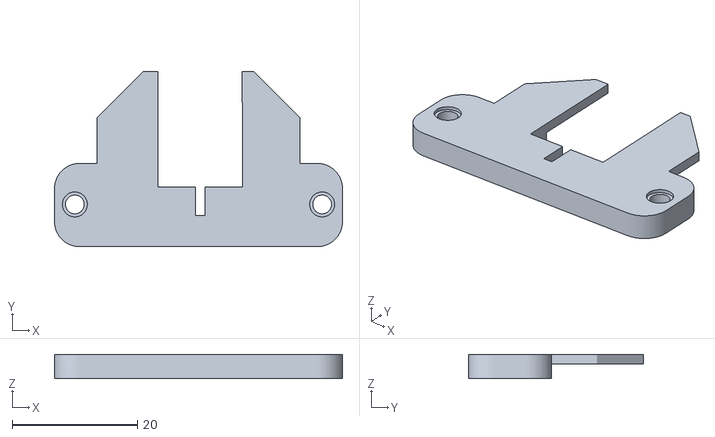
[picture p116: CAD file, 2024-09-20]
1 - Physical Unit/0 - Casing/connector_retention_v4.stl
46.0 x 28.0 x 3.84
