TheCosmicNebula/ClioIVDigitalDash/1 - Physical Unit/0 - Casing/pin_v2.stl

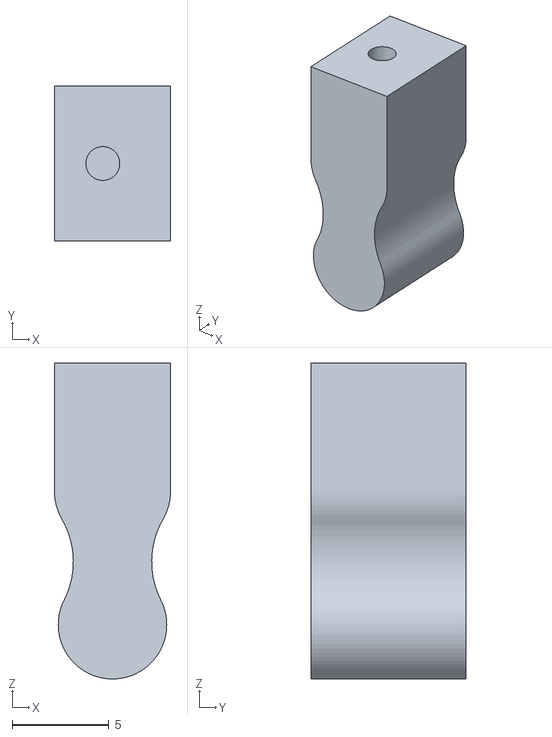
[picture p117: CAD file, 2024-09-13]
1 - Physical Unit/0 - Casing/pin_v2.stl
6.00 x 8.00 x 16.3
