TheCosmicNebula/ClioIVDigitalDash/1 - Physical Unit/0 - Casing/fan_duct_v3.stl

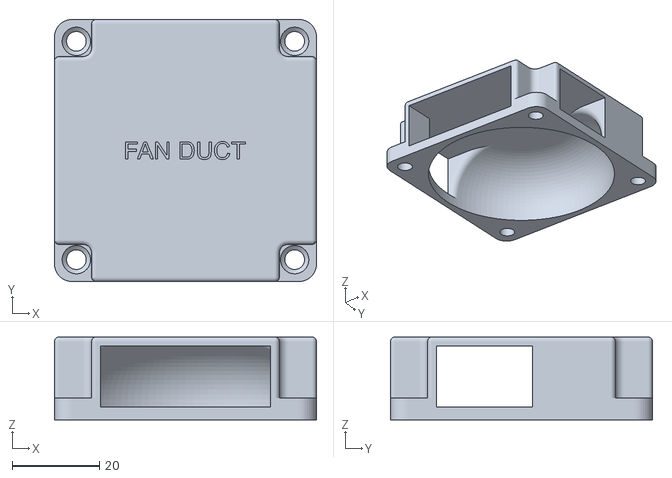
[picture p118: CAD file, 2024-09-12]
1 - Physical Unit/0 - Casing/fan_duct_v3.stl
60.0 x 60.0 x 19.0
