TheCosmicNebula/ClioIVDigitalDash/1 - Physical Unit/0 - Casing/ss/back_cover_left_v3.stl

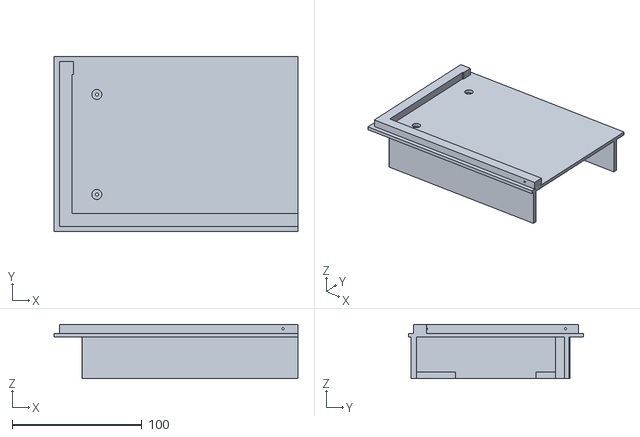
[picture p119: CAD file, 2024-09-13]
1 - Physical Unit/0 - Casing/ss/back_cover_left_v3.stl
187.9 x 135.0 x 41.7
