TheCosmicNebula/ClioIVDigitalDash/1 - Physical Unit/0 - Casing/ss/back_cover_right_v3.stl

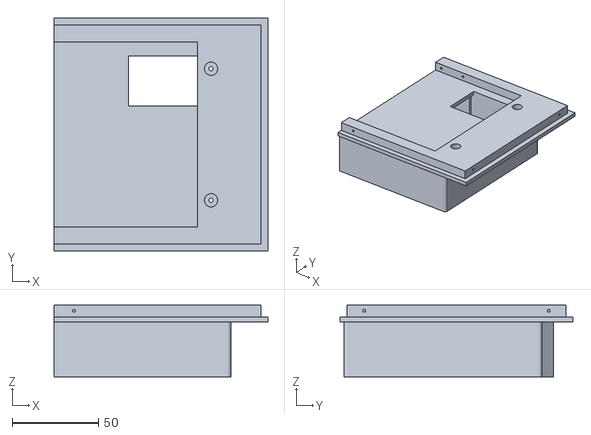
[picture p120: CAD file, 2024-09-13]
1 - Physical Unit/0 - Casing/ss/back_cover_right_v3.stl
124.1 x 135.0 x 41.7
