TheCosmicNebula/ClioIVDigitalDash/1 - Physical Unit/0 - Casing/ss/pin_v1.stl

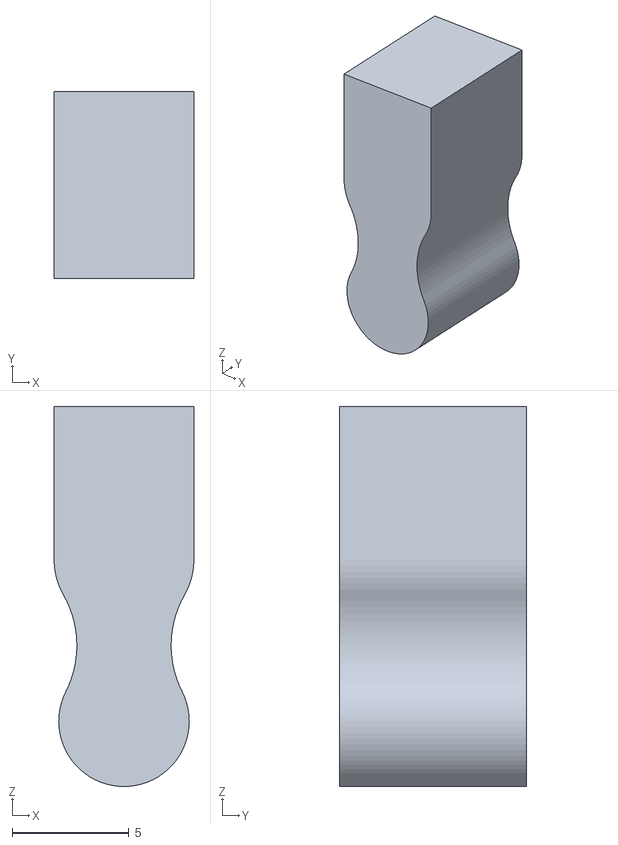
[picture p121: CAD file, 2024-09-13]
1 - Physical Unit/0 - Casing/ss/pin_v1.stl
6.00 x 8.00 x 16.3
