TheCosmicNebula/ClioIVDigitalDash/1 - Physical Unit/0 - Casing/ss/rear_shell_right_1.stl

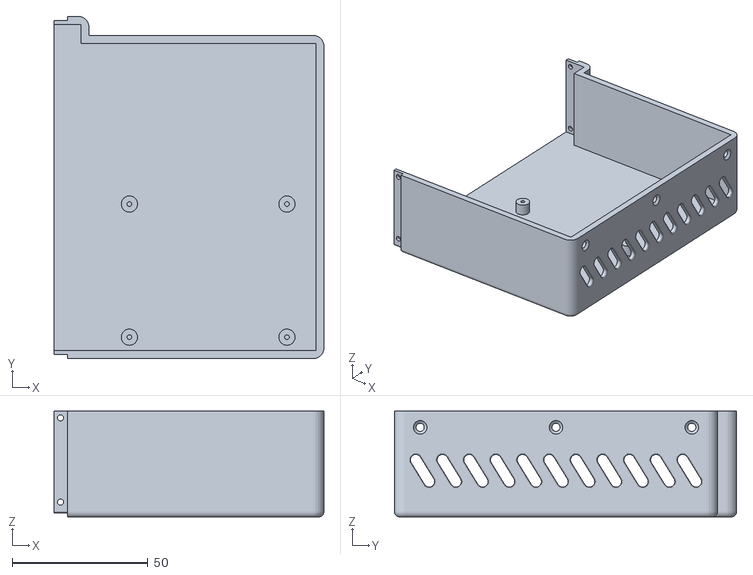
[picture p122: CAD file, 2024-09-12]
1 - Physical Unit/0 - Casing/ss/rear_shell_right_1.stl
99.4 x 126.0 x 39.0
