TheCosmicNebula/ClioIVDigitalDash/1 - Physical Unit/0 - Casing/ss/connector_retention_v3.stl

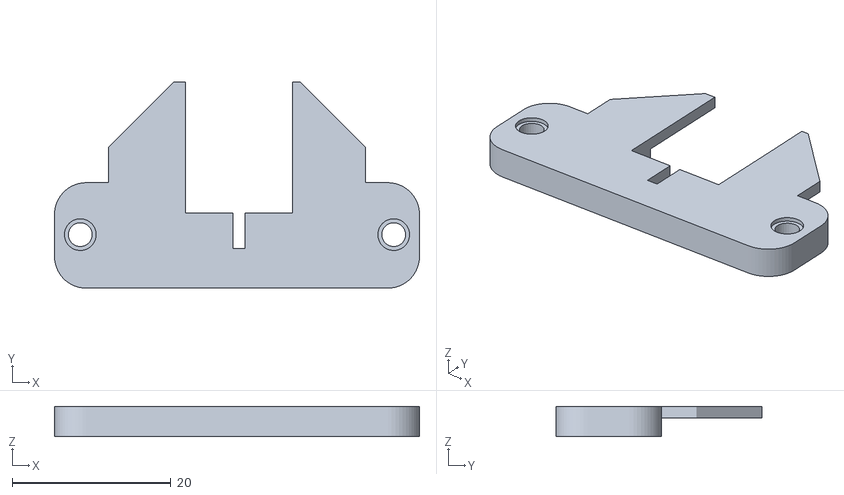
[picture p123: CAD file, 2024-09-12]
1 - Physical Unit/0 - Casing/ss/connector_retention_v3.stl
46.0 x 26.0 x 3.84
