TheCosmicNebula/ClioIVDigitalDash/1 - Physical Unit/0 - Casing/ss/rear_shell_left_v8.stl

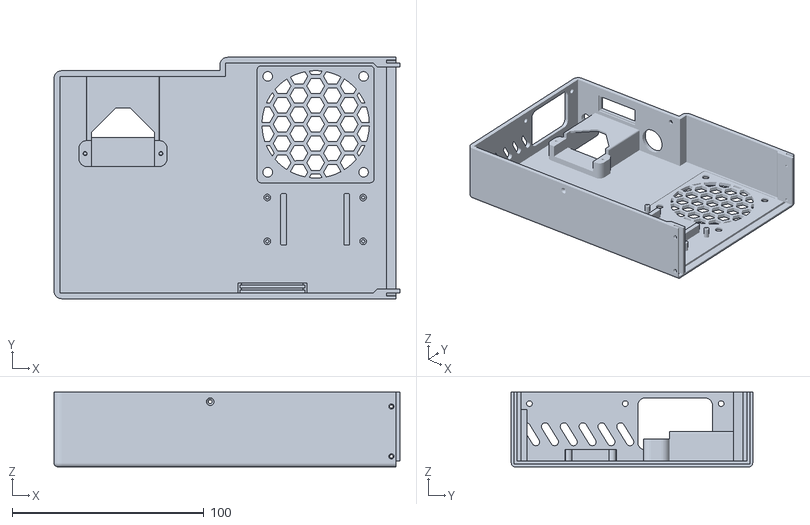
[picture p124: CAD file, 2024-09-12]
1 - Physical Unit/0 - Casing/ss/rear_shell_left_v8.stl
180.5 x 126.0 x 39.0
